DasuRathnayaka/L1-Hardware-Project/Docs/Proposal/L1 Hardware Project v2.pptx

## Food and Pharmaceutical Items Delivery Monitoring Device

IN 1900 (ICT Project)

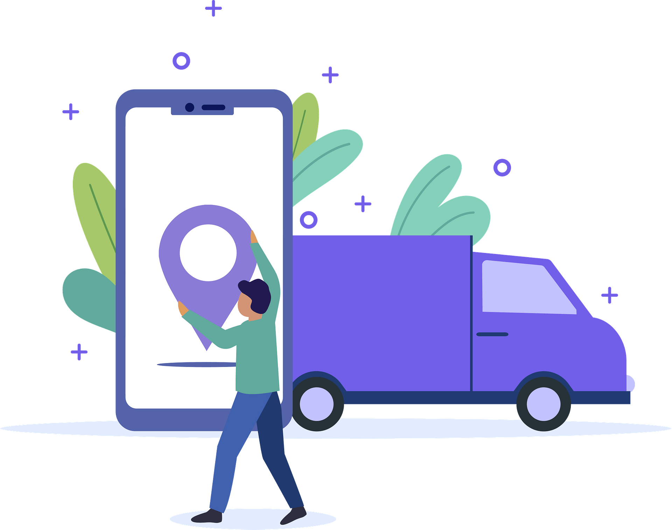
[picture p60: figure]

Group 47

Hardware Project

Notes: Nowadays we have identified many problems related to Food and Pharmaceutical items delivery mechanism. To overcome from these problems we have decided to make a device. This device is “Food and Pharmaceutical items delivery Monitoring Device”.....

## Group Members

Name | Registration Number | Photos
P.A.U.D. Herath (Team Leader) | 204074M
D.M.B.M. Dissanayake | 204047J
P.H.P. Jayathilaka | 204087F
S.P.S.N. Pathirana | 204150T
A.M.D.B.Rathnayaka | 204179N


Notes: These are our group members.

## Problem in brief

When delivering food and pharmaceutical items, we identified problems in three different sides.
1. Related to food and medicine.
2. Related to driver.
3. Related to vehicle.

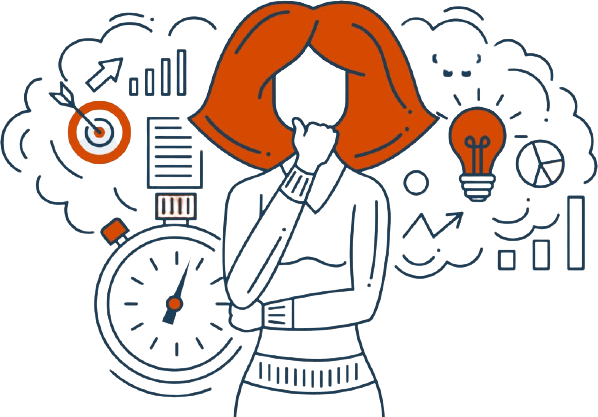
[picture p61: figure]

Notes: Our target is to give a solution from the companies side. Therefore we found out all the problems from the company’s side.
Because we are designing this device aiming a Food or pharmaceutical items delivery company.

## Related to food and medicine

- When the vehicle moves high speed the food and pharmaceutical items get damaged.
- It is hard to maintain the optimal temperature for these items. If we failed to maintain the optimal temperature the chemical state of the drugs can be changed.

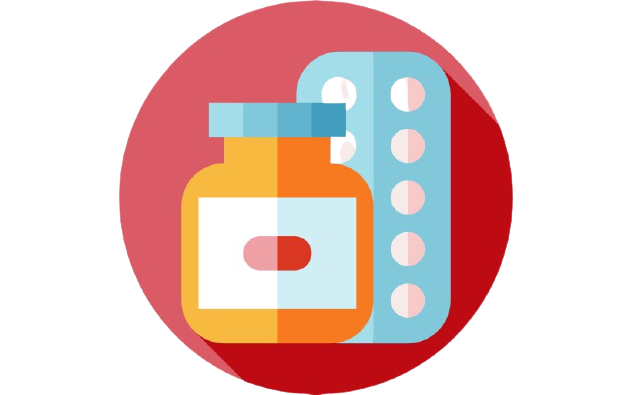
[picture p62: figure]

Notes: damage the containers
Optimal temperature - related to foods :spoil them.
related to drugs :change Chemical state of the drugs

## 2. Related to driver

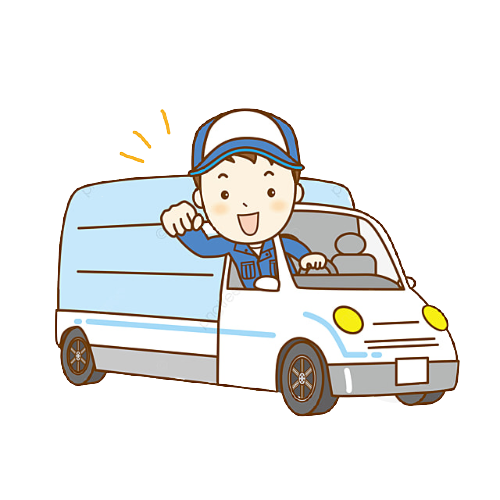
[picture p63: figure]

- Some drivers drive high speed.
- Drivers use liquor in the vehicle and also they smoke in the vehicle.
- Using the vehicles for their private purposes.
- After damaging the vehicle some drivers do not inform the company.
- Even though the drivers are good they can be charged without any reason.

Notes: Liquor : If the vehicle caught by police or if the vehicle met with an accident in such instances using of liquor and high speed will be the reason. In our device there is a mechanism to monitor the speed of the vehicle and alcohol usage.

Damaging the vehicle :

## 3. Related to vehicle

- After the vehicle met with an accident there is not a proper mechanism to inform that to the company.
- If a vehicle is stolen there is not a way to track the vehicle’s location.

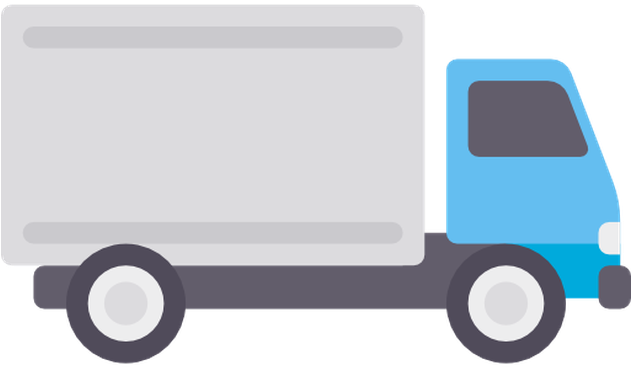
[picture p64: figure]

## Project Aim & Objectives

Aim:
- Make the Food and Pharmaceutical Items Delivery monitoring process efficiently.

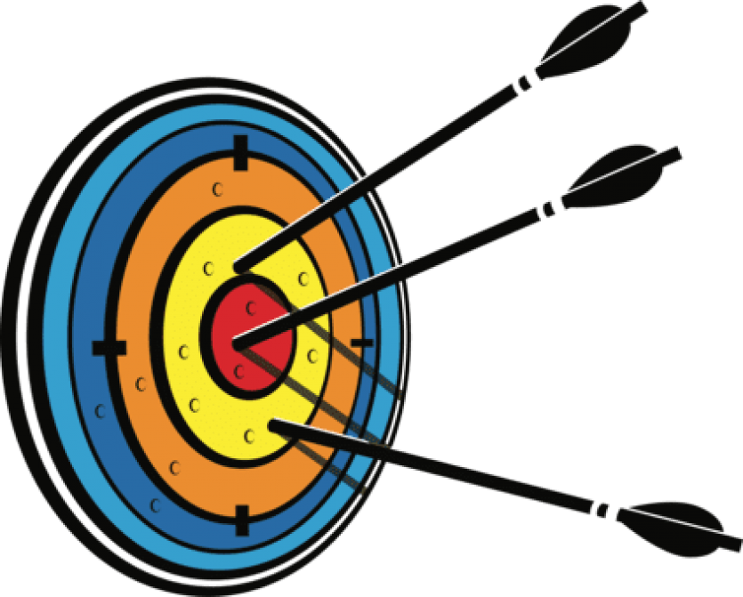
[picture p65: figure]

Notes: These days also there is a Food and pharmaceutical items delivery mechanism.

## Objectives:

- Transport the pharmaceutical and food items safely.
- Avoid the disorders which are done by drivers.
- The company owners can monitor delivery mechanism always.

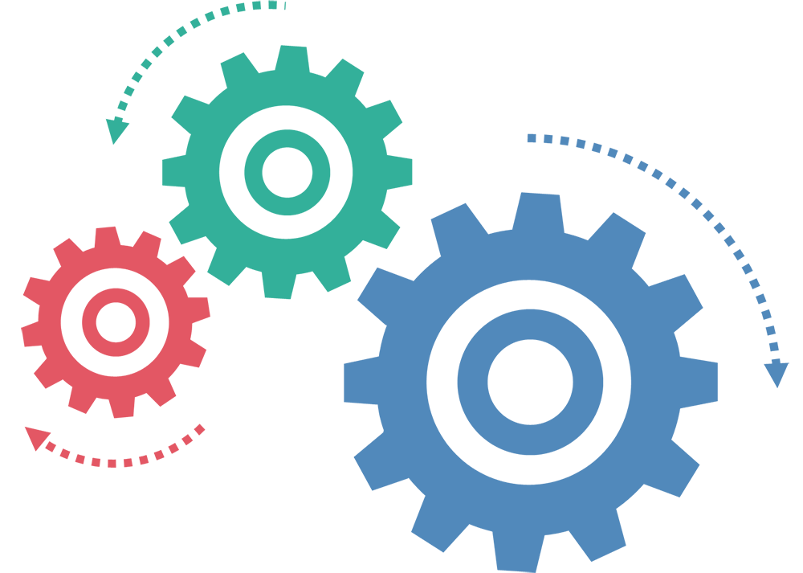
[picture p66: figure]

## Slide 9

Proposed Solution

Input

Process

Micro Controller

GPS Location Tracking

Database Access

Send SMS

Process Sensor Inputs

Output

Temperature Sensor

Temperature

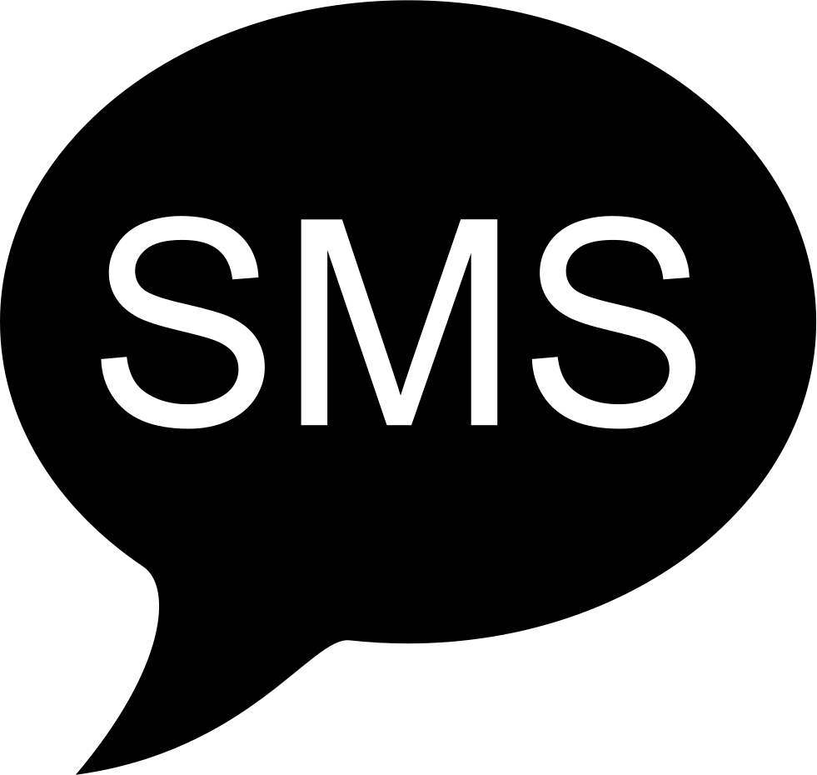
[picture p67: figure]
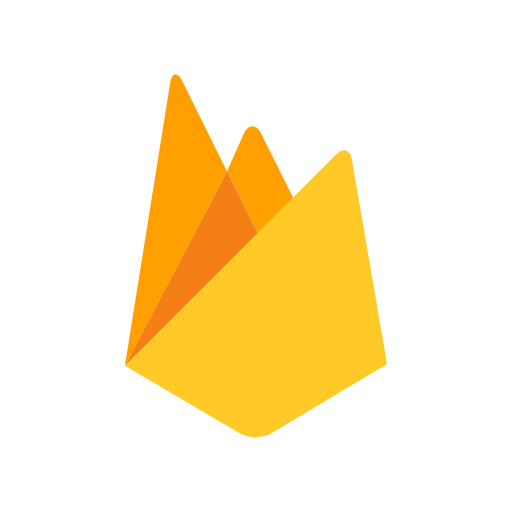
[picture p68: figure]

Firebase
Database

GPS Sensor

GPS Coordinates

Alert Signals

GSM GPRS Module

Keypad

Key Input

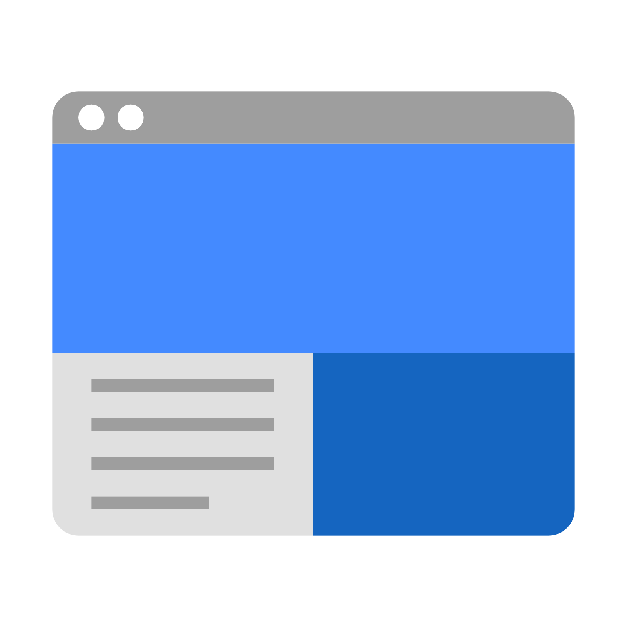
[picture p69: figure]

Web Page

Alcohol Sensor

Alcohol Sense

Alert Signals

Wi-Fi Module

Smoke Sensor

Smoke Sense

Shock Sense

Alert Signal

LCD Display

Shock Sensor

Speed Sensor

Speed

## Resources (Software)

- Proteus
- Microchip Studio
- Firebase Realtime Database

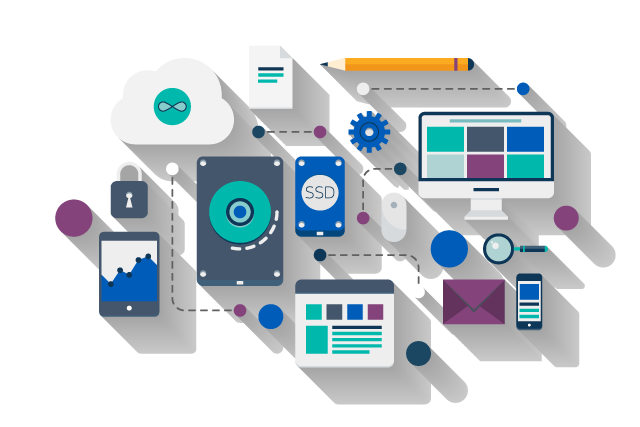
[picture p70: figure]

## Resources (Hardware)

- Atmega32 microcontroller
- Temperature sensor
- Shock sensor
- Alcohol sensor
- Smoke sensor
- Speed sensor
- Keypad

- GPS module
- Wi fi Module
- GSM module
- LCD display

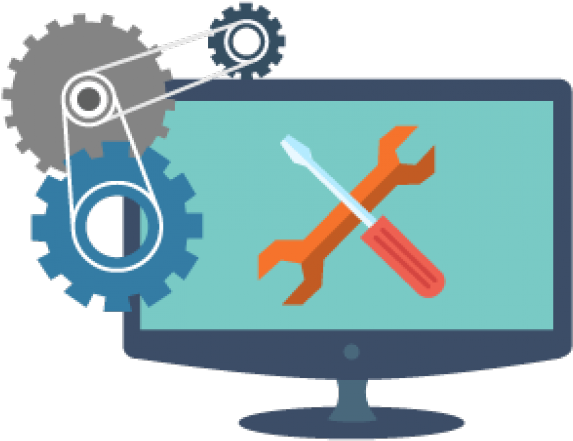
[picture p71: figure]

Notes: We use …………………………………………. As hardwares.

## Cost Estimation

Component | Unit Price | Quantity | Price (LKR)
Atmega32 Microcontroller (https://lankatronics.com/Atmega32A-PU-PDIP) | 550 | 1 | 550
Membrane Keypad - (https://lankatronics.com/Membrane-Keypad-16-key) 16 Key (https://lankatronics.com/Membrane-Keypad-16-key) | 180 | 1 | 180
2 Pin Switch (https://lankatronics.com/Rocker-Switch-ON-OFF) | 15 | 2 | 30
NEO-6M GPS Module (https://lankatronics.com/index.php?route=product/product&product_id=469&search=gps&description=true) | 1850 | 1 | 1850
Liquid Crystal 16x2 Display Module (https://lankatronics.com/index.php?route=product/product&product_id=480) | 300 | 1 | 300
SIM800C GSM GPRS Module | 1450 | 1 | 1450
801S Vibration / Shock Sensor | 500 | 1 | 500

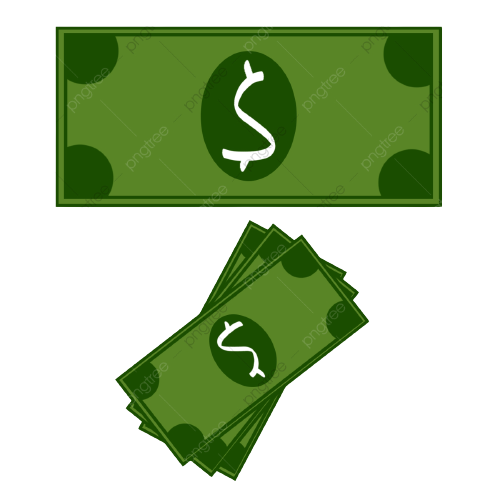
[picture p72: figure]

## Cost Estimation (Contd.)

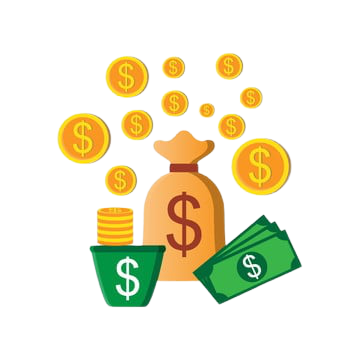
[picture p73: figure]

Component | Unit Price | Quantity | Price (LKR)
Mq3-Alcohol Sensor Module | 350 | 1 | 350
12V 2000mAh Li-Po Battery (https://microchip.lk/product/12v-2000mah-rechargeable-lithium-polymer-battery-li-po-lipo-li-po/) | 1750 | 1 | 1750
LM35 Temperature sensor | 180 | 1 | 180
ESP8266-wifi-serial-transceiver-module | 460 | 1 | 460
Total | | | 7600

Lankatronics (Pvt) Ltd (https://lankatronics.com), Microchip.lk

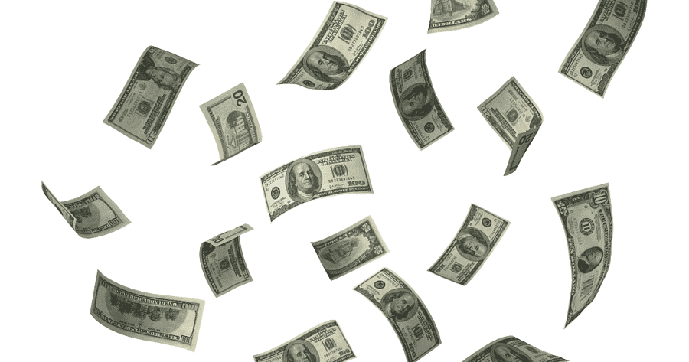
[picture p74: figure]
