DasuRathnayaka/L1-Hardware-Project/Code/Camera Stand/L1-Hardware-Project/src/defines.h

/*
 * pins.h
 *
 * Created: 10/19/2021 2:04:21 PM
 * 
 */ 

#ifndef DEFINES_H
#define DEFINES_H

#define F_CPU 8000000UL

#include <stdio.h>
#include <stdlib.h>
#include <avr/io.h>
#include <util/delay.h>
#include <avr/interrupt.h>
#include <stdbool.h>
#include <stdint.h>

#include "utils/nRF24L01/spi_config.h"
#include "utils/nRF24L01/avr_spi.h"
#include "utils/nRF24L01/nrf24l01_reg.h"
#include "utils/nRF24L01/nrf24l01_config.h"
#include "utils/nRF24L01/nrf24l01.h"


typedef struct Pin {
	uint8_t pin;
	char port;
} Pin;

typedef struct Coordinate {
	double longitude;
	double latitude;
} Coordinate;

#define INPUT 0
#define OUTPUT 1
#define INPUT_PULLUP 2

#define HIGH 1
#define LOW 0

// I2C
#define MY_ADDRESS 0xCC
#define READ 1
#define WRITE 0

//GPS related
#define Buffer_Size 150
#define degrees_buffer_size 20

// Mode
typedef enum {
	UP_DOWN = 0,
	LEFT_RIGHT,
	FORW_BACKW,
	SIREN,
	MODE
} uint8_mode;

Coordinate destination;

int timer0_overflow; // Overflow for Timer 1

unsigned long ultrazonic_pulse;

#define PI 3.142857
unsigned char i;		//Max width of the LCD Display.
#define RATE 250					//Rate of scrolling.
void WaitMs(unsigned int ms);		//Declaration of delay routine used.
void usart_init();
unsigned int usart_getch();
char value,lati_value[15],lati_dir, longi_value[15], longi_dir;
char* tempValue;
char output[100];

const Pin A0;
const Pin A1;
const Pin A2;
const Pin A3;
const Pin A4;
const Pin A5;
const Pin A6;
const Pin A7;

const Pin B0;
const Pin B1;
const Pin B2;
const Pin B3;
const Pin B4;
const Pin B5;
const Pin B6;
const Pin B7;

const Pin C0;
const Pin C1;
const Pin C2;
const Pin C3;
const Pin C4;
const Pin C5;
const Pin C6;
const Pin C7;

const Pin D0;
const Pin D1;
const Pin D2;
const Pin D3;
const Pin D4;
const Pin D5;
const Pin D6;
const Pin D7;

// Main initialization and loop
void sys_init(void);
void sys_loop(void);

// Basic definitions
uint8_t char_to_int(char val);
volatile uint8_t* select_register(char portChar, volatile uint8_t* A, volatile uint8_t* B, volatile uint8_t* C, volatile uint8_t* D);
int pin_mode(Pin pin, int mode);
unsigned long time_ms();
unsigned long time_us();

// Digital utilities
int digital_write(Pin pin, int level);
int digital_read(Pin pin);

// PWN
void PWM_init(void);
int PWM_write_reg(void *regi, int dutyCyle);
int PWM_write(Pin pin, int dutyCyle);

// Display
void LCD_init();
void LCD_msg(char *c);
void LCD_clear_msg(char* c);
void LCD_clear();
void LCD_line_1();
void LCD_line_2();
void LCD_num(double num);
void LCD_char(char c);

// UART
void UART_init(long USART_BAUDRATE);
unsigned char UART_RxChar();
void UART_TxChar(char ch);
void UART_SendString(char *str);

// Keypad
char key_char();
void key_string(char buffer[], int buff);

// Ultrasonic Sensor
void ultrazonic_init();
int ultrazonic_error();
double ultrazonic_distance(void);

// SPI
const Pin SLAVE_SS_0;
const Pin MOSI;
const Pin MISO;
const Pin SCK;
void SPI_master_init();
void SPI_slave_init();
void SPI_select_slave(Pin SS);
void SPI_deselect_slave(Pin SS);
unsigned char SPI_tranceiver(unsigned char data);
int SPI_check_available();
unsigned char SPI_read();
void SPI_write(unsigned char data);

// I2C
void I2C_master_init();
void I2C_slave_init(unsigned char address);
void I2C_start();
void I2C_stop();
void I2C_write(unsigned char x);
void I2C_select_slave(unsigned char address, int mode);
void I2C_listen(void);
unsigned char I2C_read();
void I2C_slave_read_buffer(char* buffer, int length);
void I2C_master_write_buffer(unsigned char address, char* buffer, int length);

//GPS module
void GPS_init();
char* get_lati_str();
char* get_longi_str();
float get_lati_float();
float get_longi_float();
int angle_from_north(float lati_input, float longi_input);
char* itoa(int num, char* buffer, int base);
void Double2String(char *output,double val,int n);
char c[15];

// Motors
void motor_init();
void setM2Speed(int speed);
void setM1Speed(int speed);
void drive(int m1Speed, int m2Speed);

// Servo
void servo_init();
void servo_write(int angle);


#endif
